automote/thingSocket/Hardware/espschematics.jpg

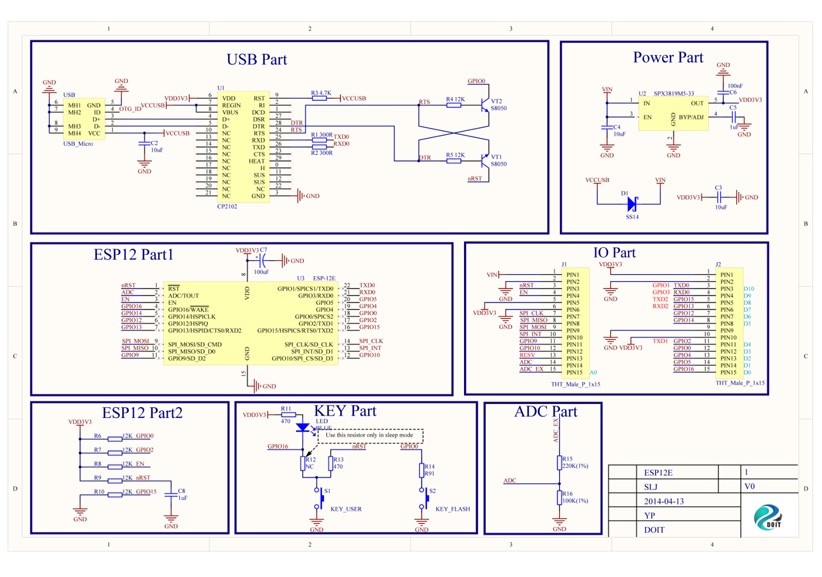
Hardware/espschematics.jpg
