automote/thingSocket/Hardware/v0.1_04-02-2016/AC220S3.3DCS-3W Henlv.jpg

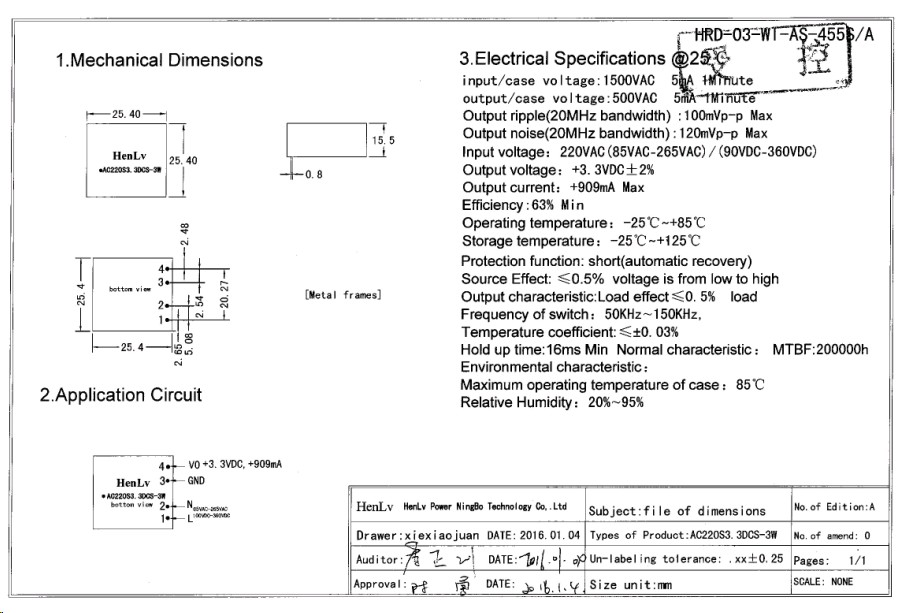
Hardware/v0.1_04-02-2016/AC220S3.3DCS-3W Henlv.jpg
