automote/thingSocket/Hardware/v0.1_04-02-2016/Images/dev-image-3.jpg

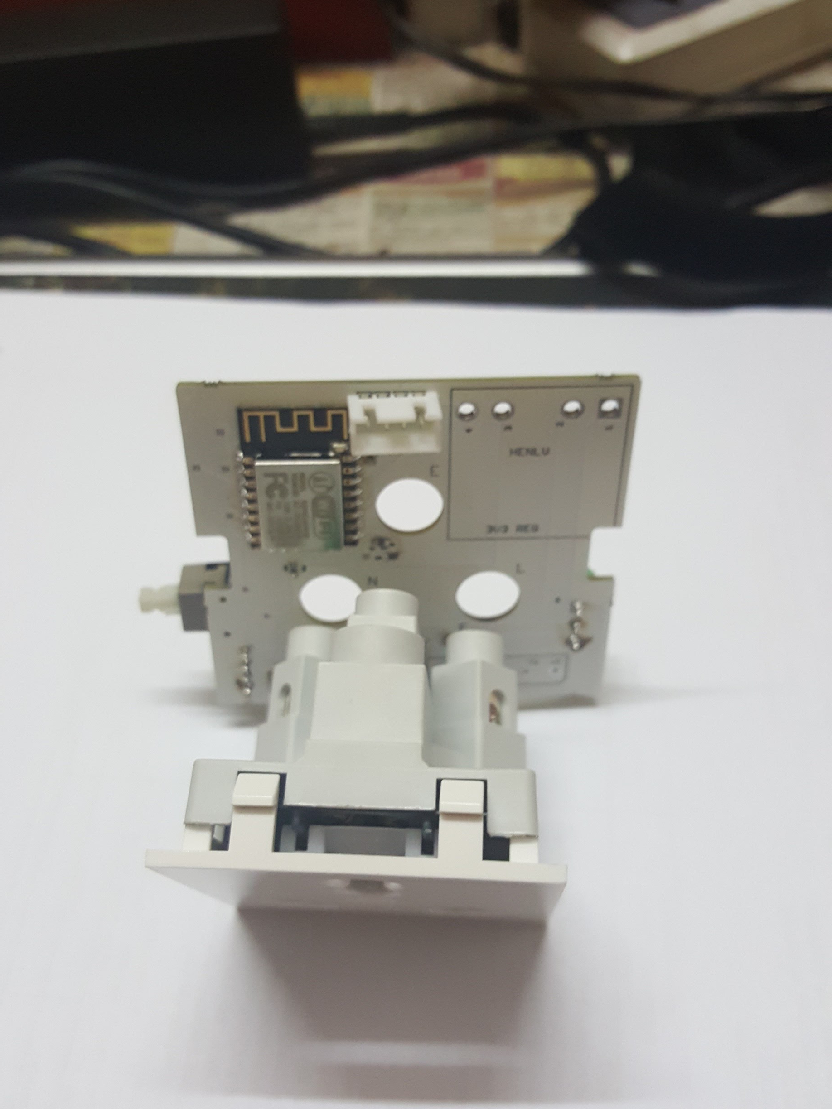
Hardware/v0.1_04-02-2016/Images/dev-image-3.jpg
